aotta/PiRTOII/Pictures/IMG_20240518_174654.jpg

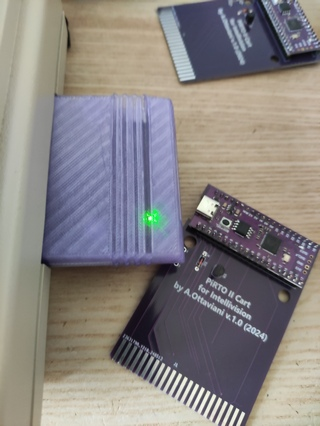
Pictures/IMG_20240518_174654.jpg
